Yohannfra/Touche/client/include/client_pinout.h

#ifndef CLIENT_PINOUT_H
#define CLIENT_PINOUT_H

#define LED_PIN 5

#define EPEE_BUTTON_PIN 3

#define NRF24L01_CE_PIN 7

#define NRF24L01_CS_PIN 8

#define VIRTUAL_PIN_IN 2

#define VIRTUAL_PIN_OUT 4

#endif // CLIENT_PINOUT_H
